felixtsao/oneVR_devel/cam/XiaoYiMi/distortionXiaoYiMi.jpg

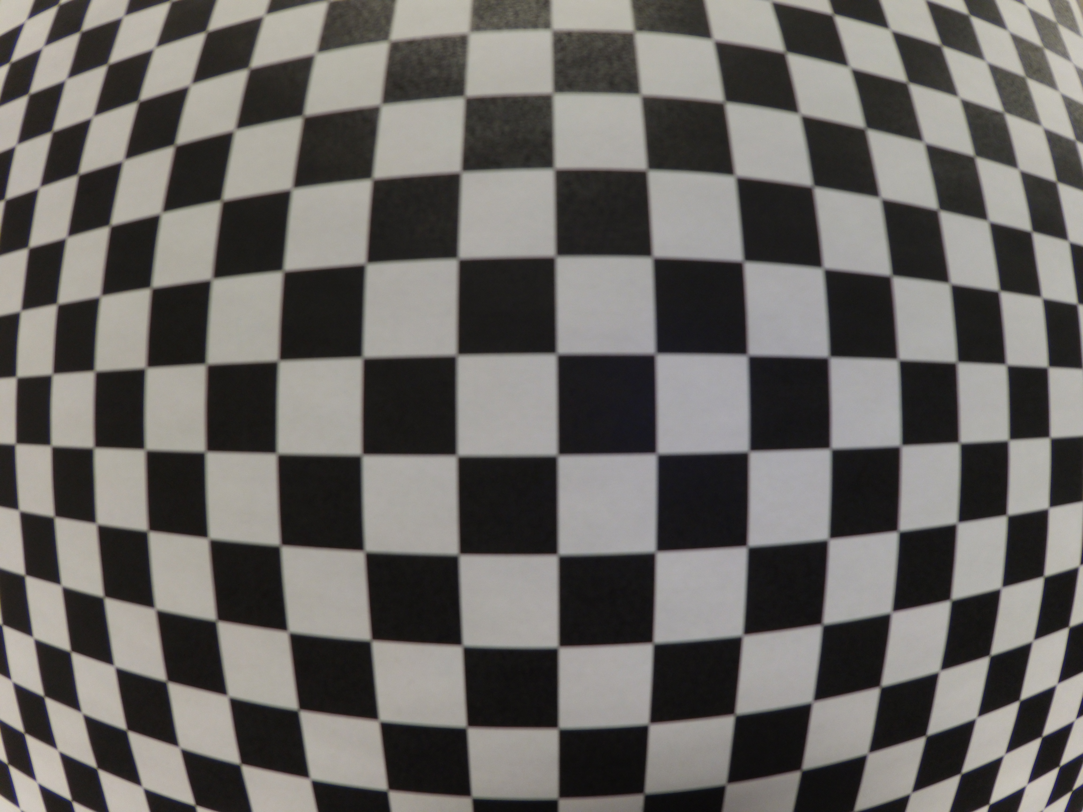
cam/XiaoYiMi/distortionXiaoYiMi.jpg
