felixtsao/oneVR_devel/img/doc/sj4000_6x_03.jpg

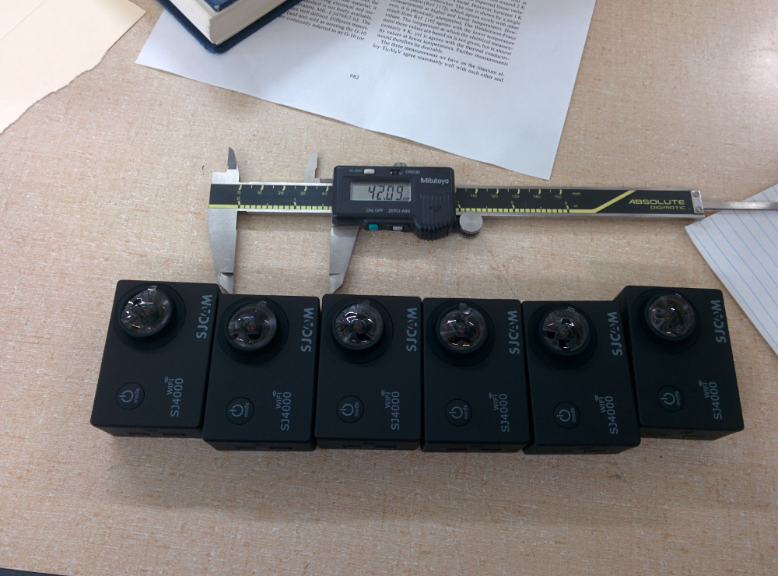
img/doc/sj4000_6x_03.jpg
