felixtsao/oneVR_devel/img/doc/sj4000_6x_v3_02.jpg

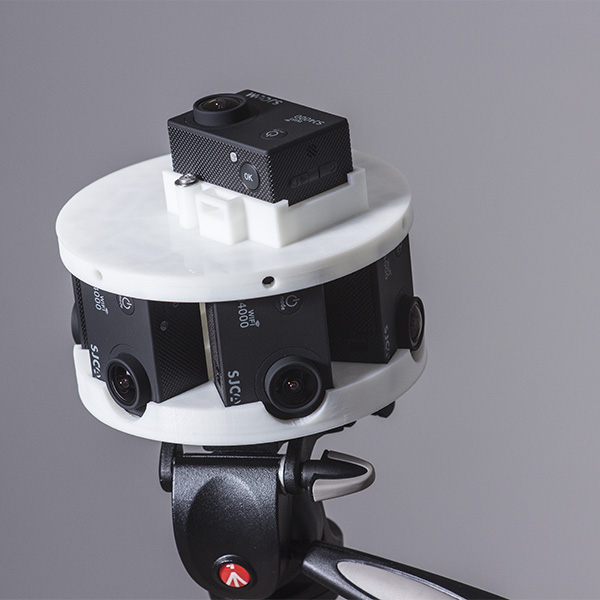
img/doc/sj4000_6x_v3_02.jpg
