felixtsao/oneVR_devel/img/pano/la/0.jpg

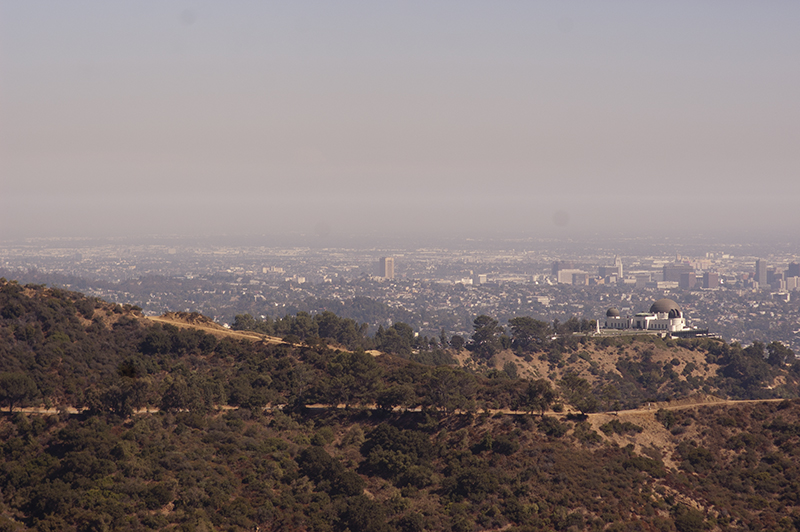
img/pano/la/0.jpg
