felixtsao/oneVR_devel/img/pano/la/1.jpg

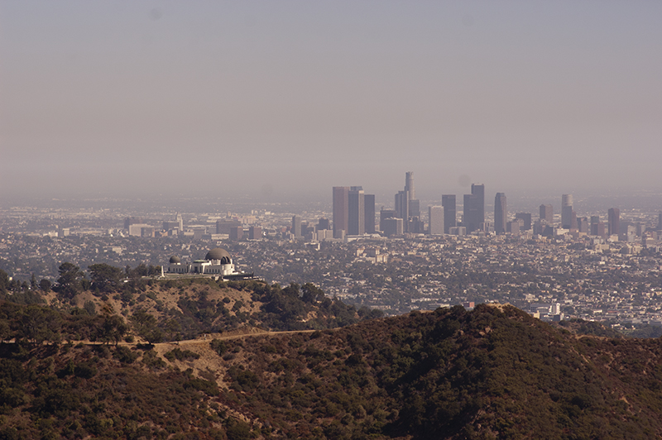
img/pano/la/1.jpg
