felixtsao/oneVR_devel/img/pano/la/2.jpg

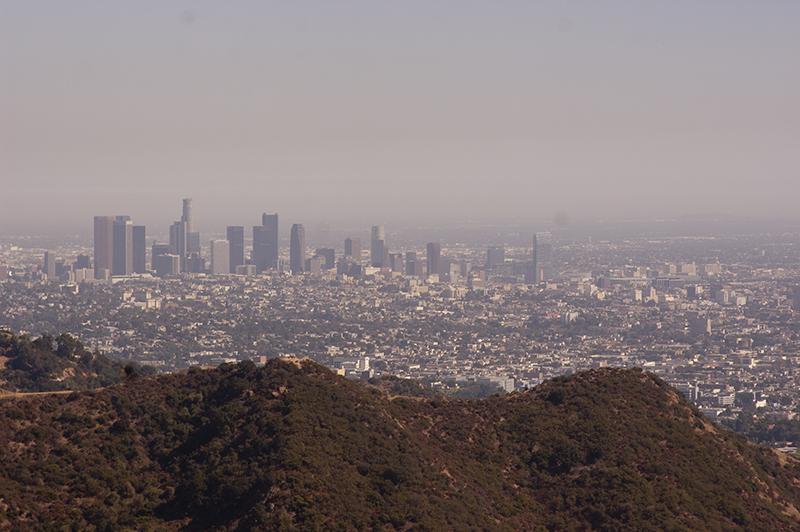
img/pano/la/2.jpg
