felixtsao/oneVR_devel/img/pano/la/3.jpg

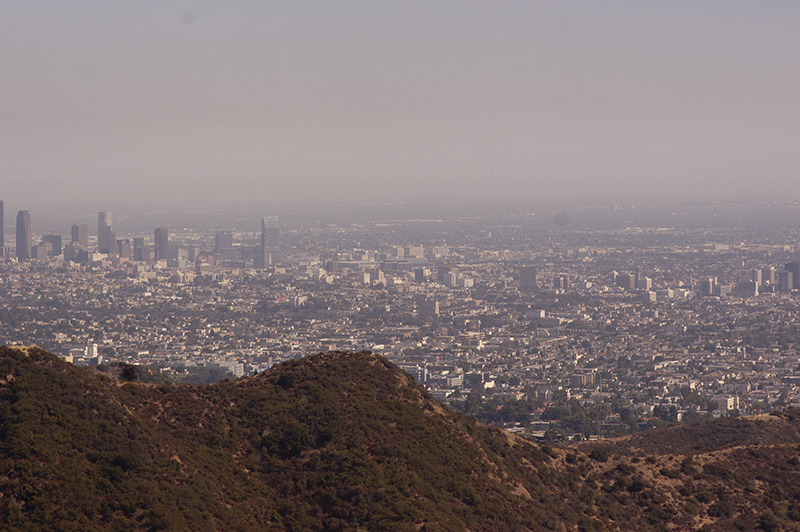
img/pano/la/3.jpg
