felixtsao/oneVR_devel/img/pano/la/4.jpg

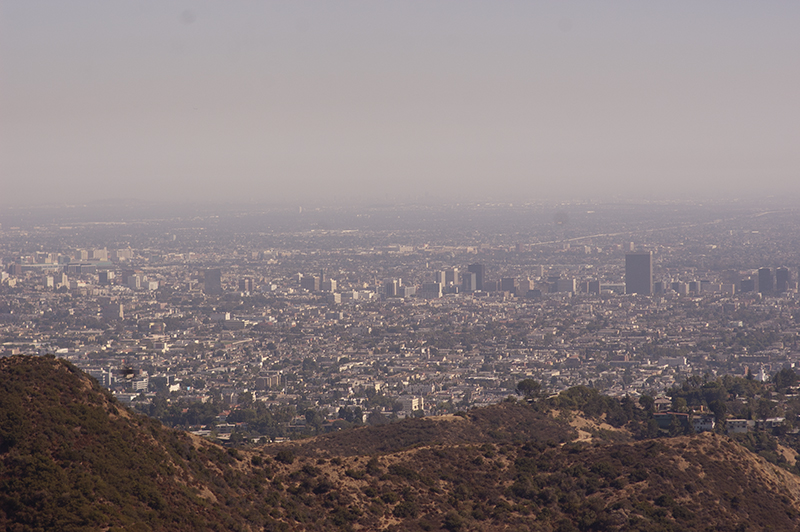
img/pano/la/4.jpg
