felixtsao/oneVR_devel/img/pano/la/5.jpg

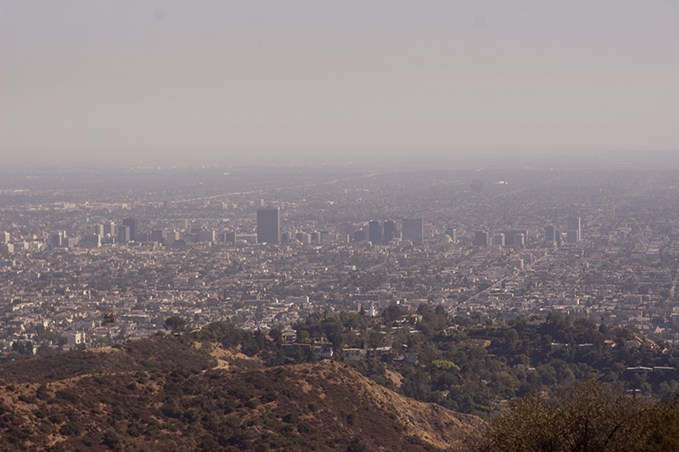
img/pano/la/5.jpg
