felixtsao/oneVR_devel/img/pano/la/6.jpg

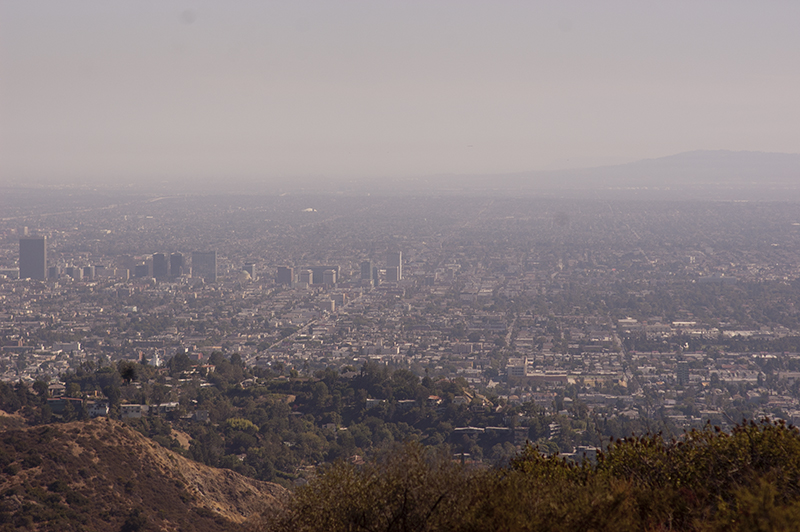
img/pano/la/6.jpg
