felixtsao/oneVR_devel/img/pano/la/7.jpg

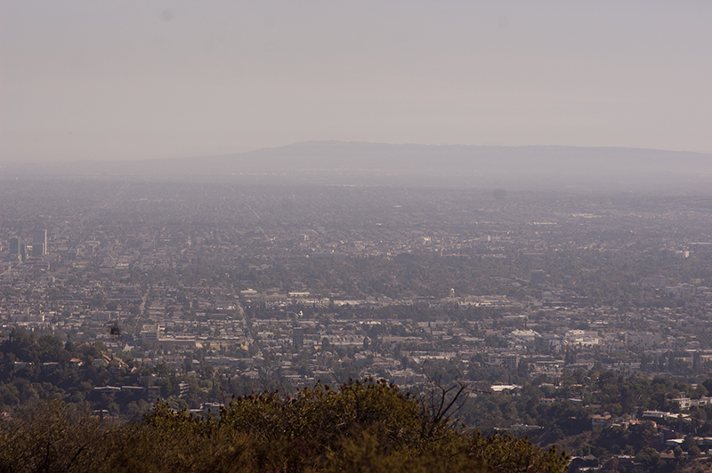
img/pano/la/7.jpg
