felixtsao/oneVR_devel/img/pano/la/8.jpg

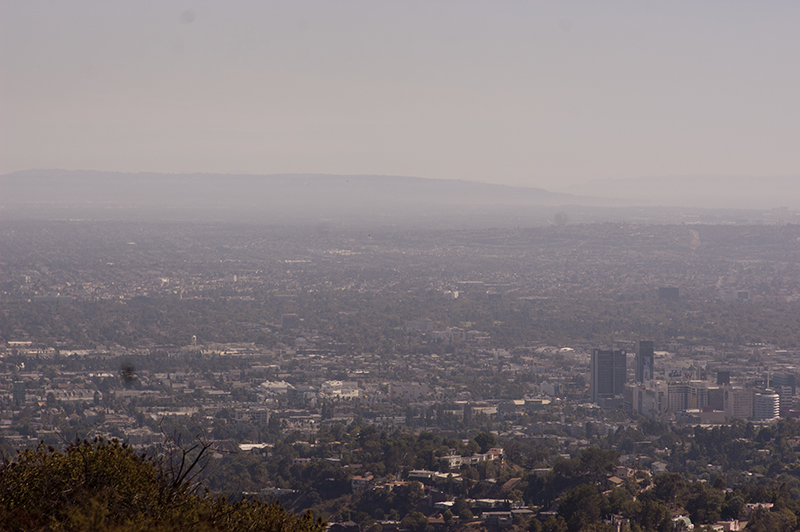
img/pano/la/8.jpg
