felixtsao/oneVR_devel/img/pano/r8/r81.jpg

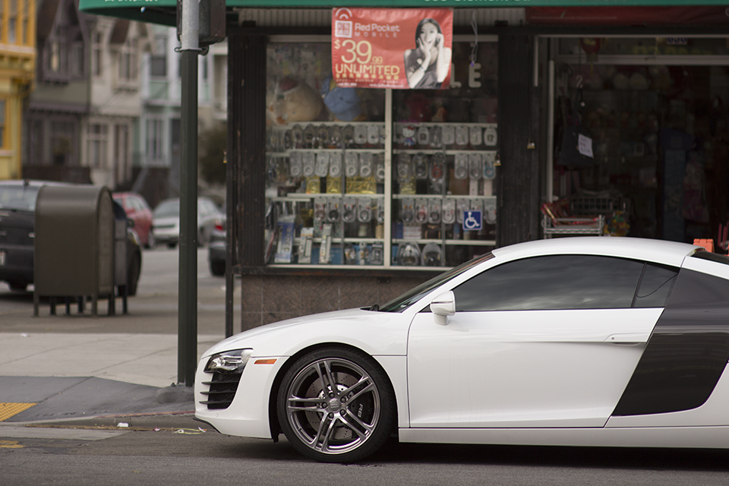
img/pano/r8/r81.jpg
