felixtsao/oneVR_devel/img/pano/r8/r82.jpg

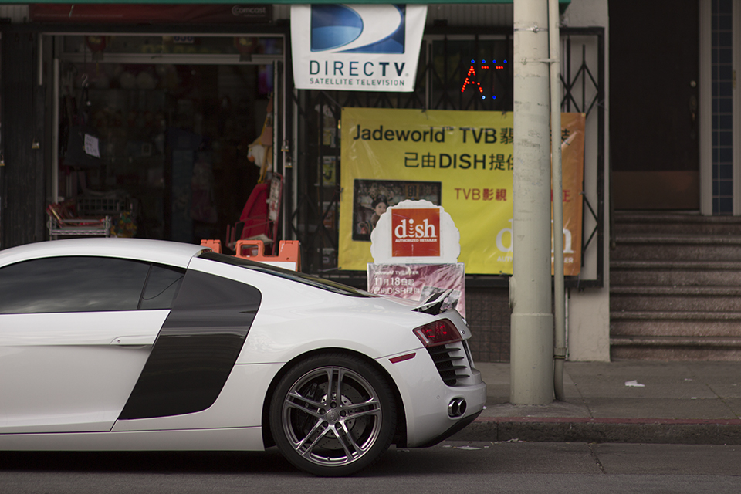
img/pano/r8/r82.jpg
