felixtsao/oneVR_devel/img/pano/sf/0.jpg

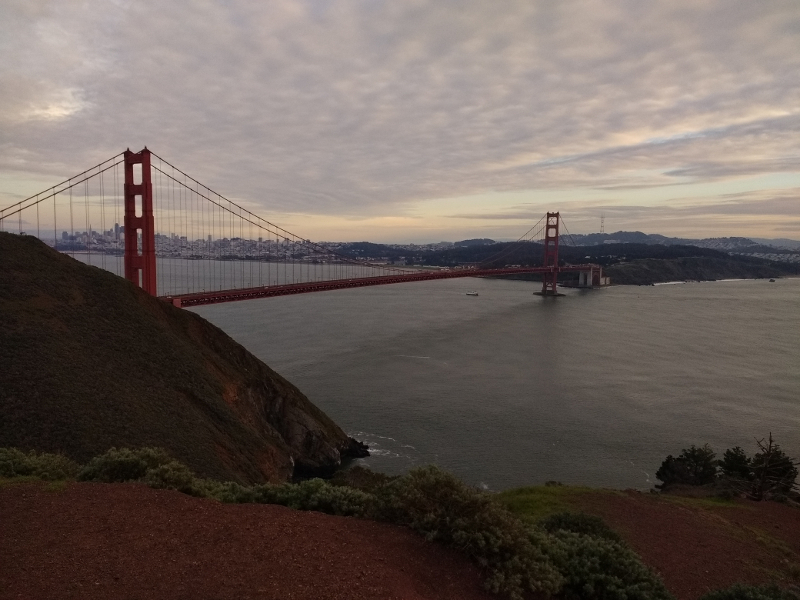
img/pano/sf/0.jpg
