felixtsao/oneVR_devel/img/pano/sf/1.jpg

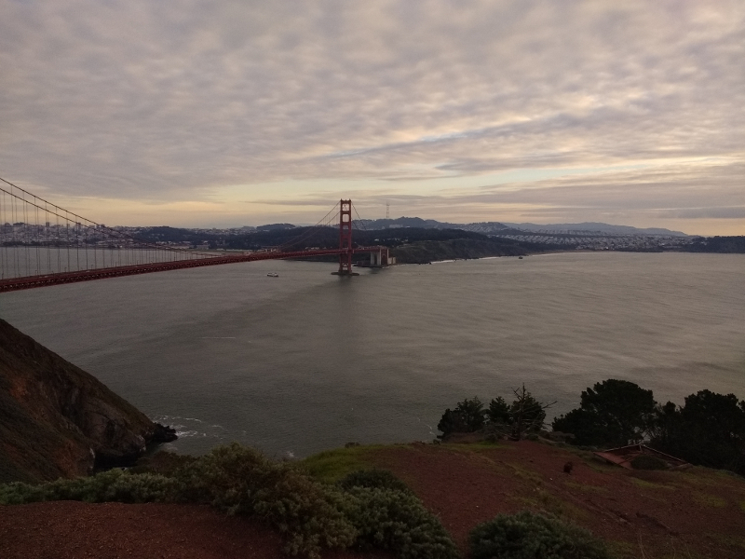
img/pano/sf/1.jpg
