felixtsao/oneVR_devel/img/pano/sf/2.jpg

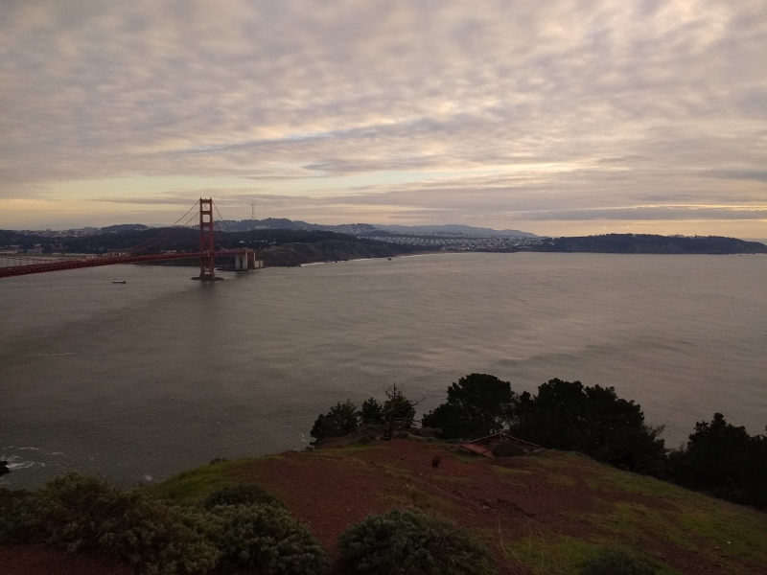
img/pano/sf/2.jpg
