felixtsao/oneVR_devel/img/pano/sf/3.jpg

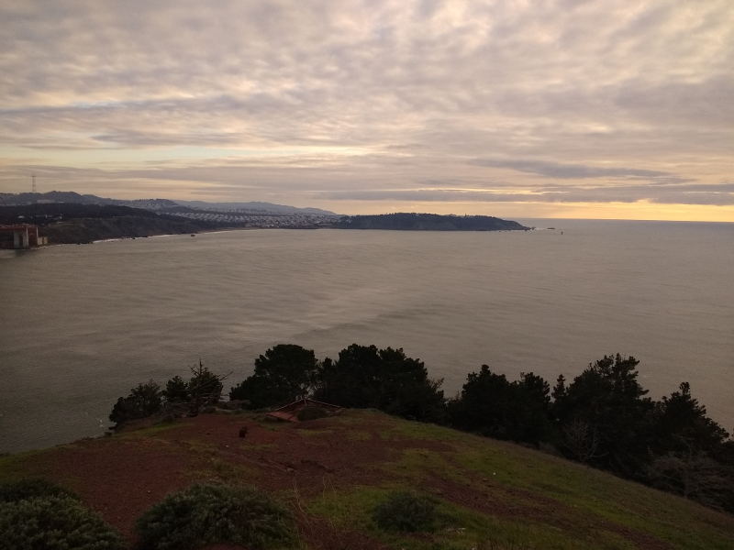
img/pano/sf/3.jpg
