felixtsao/oneVR_devel/img/pano/sf/4.jpg

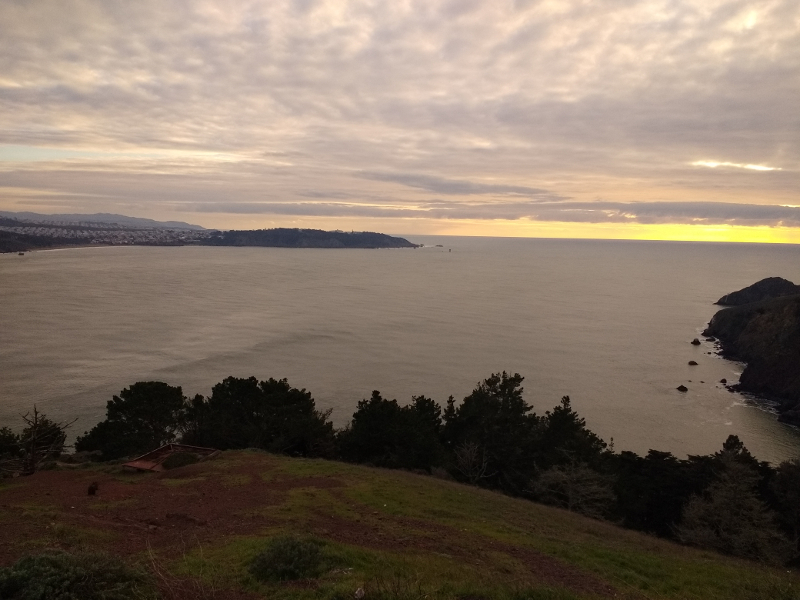
img/pano/sf/4.jpg
