felixtsao/oneVR_devel/img/pano/sf/5.jpg

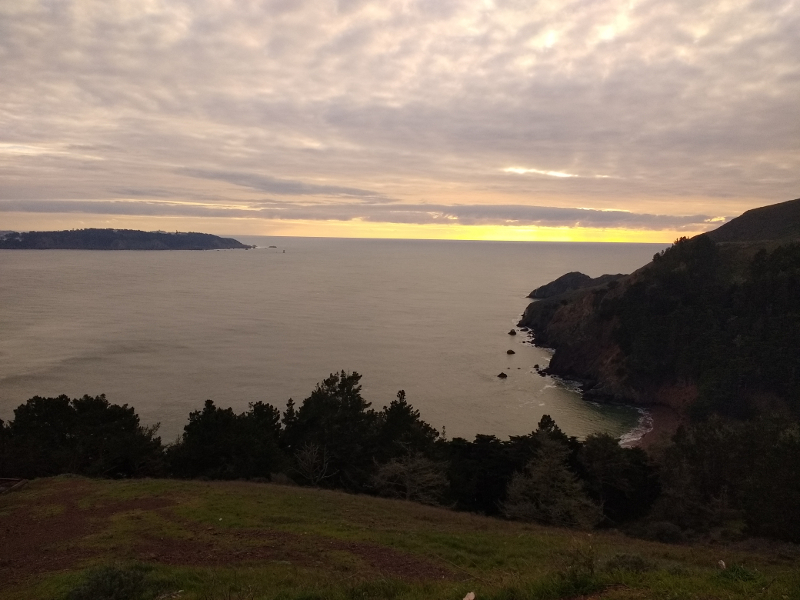
img/pano/sf/5.jpg
