felixtsao/oneVR_devel/img/pano/sf/6.jpg

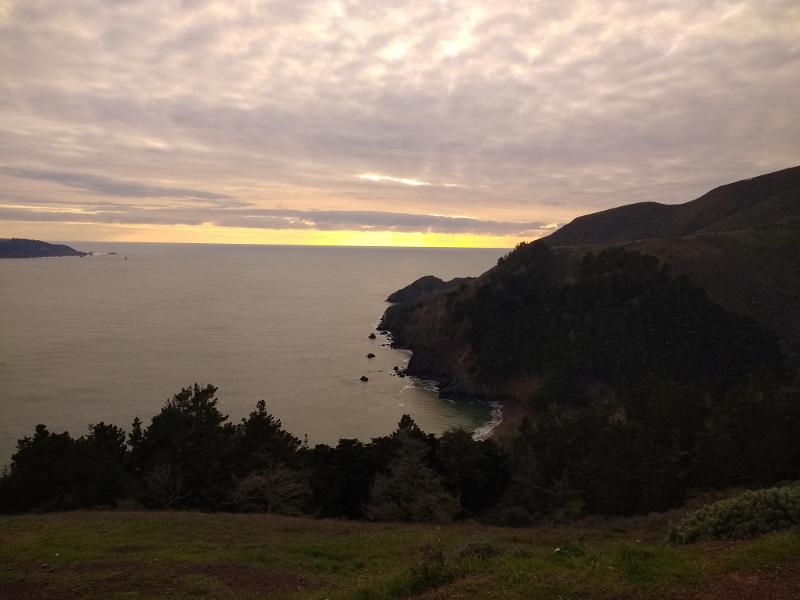
img/pano/sf/6.jpg
