felixtsao/oneVR_devel/mlab_prototype/pano.jpg

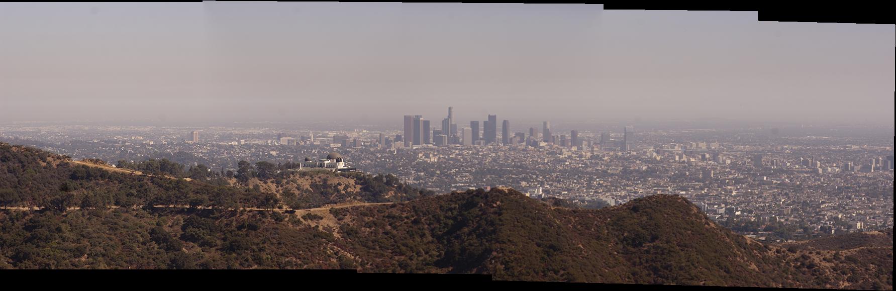
mlab_prototype/pano.jpg
