felixtsao/oneVR_devel/mlab_prototype/pano_cyl_artifacts.jpg

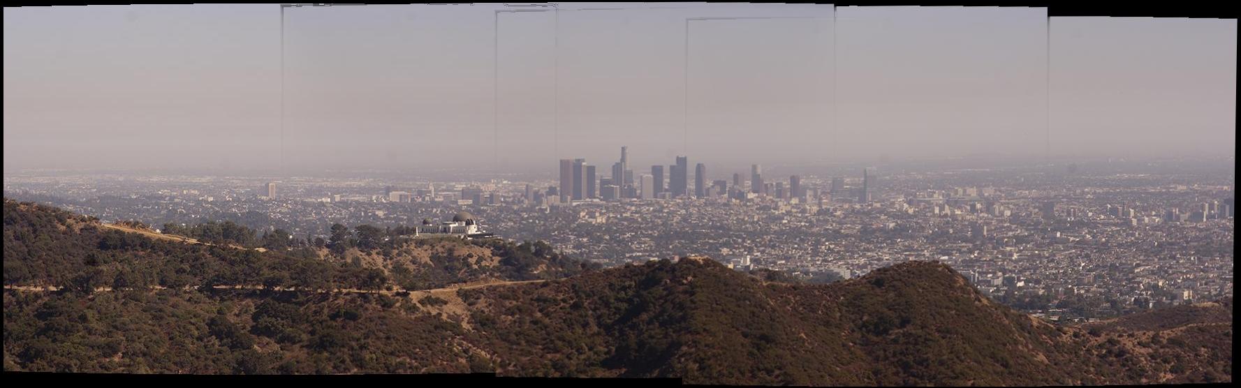
mlab_prototype/pano_cyl_artifacts.jpg
