felixtsao/oneVR_devel/viewer/img/loader.gif

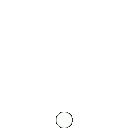
viewer/img/loader.gif
