felixtsao/oneVR_devel/viewer/img/play.png

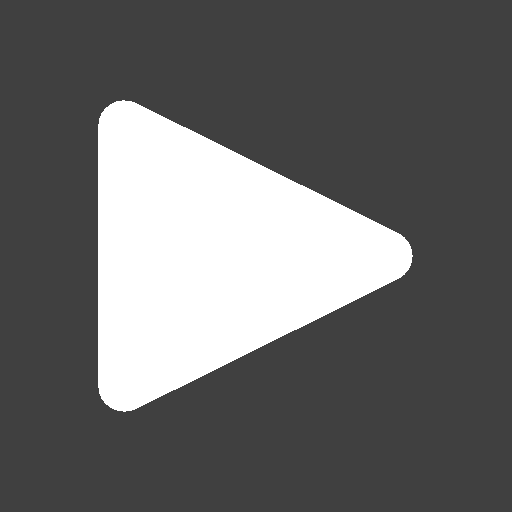
viewer/img/play.png
